MadsRudolph/62768-energy-system/report/sections/responsibility.tex

\ifdefined\mainfile\else\documentclass{article}
\input{../preamble}\begin{document}\fi

\section{Responsibility}
\label{sec:Responsability}

\begin{table}[H]
\centering
\caption{Team responsibilities in the project.}
\renewcommand{\arraystretch}{1.2}

\begin{tabular}{|c|p{8cm}|p{5cm}|}
\hline
\textbf{No.} & \textbf{Tasks} & \textbf{Person} \\
\hline
1 & Design and build the motor-generator setup & All group members \\
\hline
2 & Build and test the rectifier circuit & Nikolas P.L and Nikolas S.J \\
\hline
3 & Design and test the buck converter & Andreas S.J, Jonas B.J and Bjørn A.B  \\
\hline
4 & Design and test the boost converter & Mads R. \\
\hline
5 & Solar panel measurements and MPPT analysis & All group members \\
\hline
6 & Simulink model and PID code generation & Nikolas P.L and Andreas S.J\\
\hline
7 & System integration and final testing & All group members \\
\hline
8 & Report writing and documentation & All group members \\
\hline
\end{tabular}

\label{tab:team_responsibilities}
\end{table}

\ifdefined\mainfile\else\end{document}\fi
