MadsRudolph/62768-energy-system/report/sections/systemoverblik.tex

\ifdefined\mainfile\else\documentclass{article}\input{../preamble}\begin{document}\fi

\section{System overview and requirements}
\label{sec:systemoverblik}
% Overordnet blokdiagram (se TikZ-skabelon nedenfor) + de vigtigste krav (V1/V2/V3).
% Forklar energistrømmen: AC-generator -> transformer -> ensretter -> buck;
% solcelle -> MPPT -> lineær reg -> energilager; boost -> pulserende last.

% --- Skabelon til blokdiagram (udfyld/erstat) ---
\begin{figure}[H]
    \centering
    \begin{tikzpicture}[node distance=2.2cm and 1.6cm]
        \node[block] (gen)  {AC-generator};
        \node[block, right=of gen] (tr) {3$\times$ transformer};
        \node[block, right=of tr] (rec) {Rectifier};
        \node[block, right=of rec] (buck) {Buck 4.8\,V};
        \draw[->] (gen) -- (tr);
        \draw[->] (tr) -- (rec);
        \draw[->] (rec) -- node[above]{V1=15\,V} (buck);
    \end{tikzpicture}
    \caption{Simplified block diagram of the energy system, expanded with PV module/MPPT, energy storage, boost converter, and load).}
    \label{fig:blokdiagram}
\end{figure}

\begin{table}[H]
    \centering
    \begin{tabular}{c l l}
        \toprule
        \textbf{Node} & \textbf{Voltage} & \textbf{Requirement} \\
        \midrule
        V1 & 15\,V $\pm$1\,V  & at 100--300\,mA, hold within for 1.0\,s \\
        V2 & 10\,V $\pm$1\,V  & deliver $\geq$150\,mA, last-step 50--150\,mA \\
        V3 & 5\,V $\pm$0.5\,V & for currents $>$20\,mA \\
        \bottomrule
    \end{tabular}
    \caption{Central voltage specifications. Full list in appendiks~\ref{sec:kravsporing}.}
    \label{tab:krav-overblik}
\end{table}

\ifdefined\mainfile\else\end{document}\fi
