MadsRudolph/62768-energy-system/hardware/kicad/production/motor_power/board_preview_summary.md

# board - board summary

- Size: 104.0 x 104.0 mm
- Copper area: 7995.2 mm^2
- Holes: 181
  - 0.8 mm x 129
  - 1.0 mm x 2
  - 1.1 mm x 29
  - 1.2 mm x 2
  - 1.52 mm x 19
