MadsRudolph/62768-energy-system/docs/Project Specifications.pdf

### KRAVSPECIFIKATION FOR UDVIKLING AF ELEKTRISK ENERGISYSTEM (62768) I 3-UGERS KURSET F2022

Revisionshistorie:

V0: basis specifikation.

V1: Krav 4,5,6 er opdateret / ændret.

V2: Nyt krav om Buck og Boost konvertere er tilføjet.

V3: Krav 5 og 6 er opdateret mht. levering af strøm og belastningen ændringer.

V4: Krav 8-10 opdateret med krav om anvendelse af diskrete komponenter + krav 18 om anvendelse af Arduino platform.

Opgaveoverblik

Der skal udvikles et elektrisk energisystem s om opfylder nedenstående krav. Et blokdiagram over systemet er vist nedenfor.

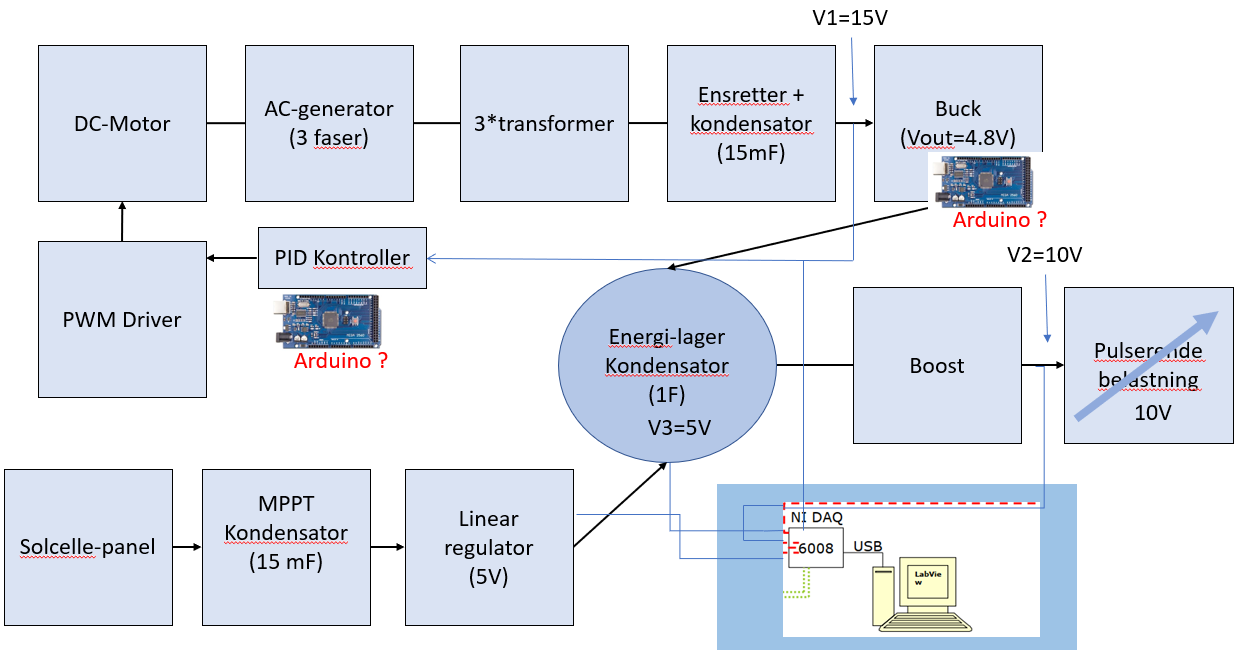
[picture p32: figure]

Krav:

Nummer: | Navn: | Beskrivelse: | Prioritet:
1 | AC-generator spænding (V1) | Den ensrettede spænding på lade-kondensatoren (V1) skal være 15 volt +/- 1 volt. For en buck-strøm på 100 mA | 1
2 | AC-generator strøm | AC-generator systemet skal kunne levere 300 mA til buck konverteren. | 1
3 | AC-generator spænding (V1) under belastning. | Ved en belastningsændring fra 100 mA til 300 mA skal spændingen (V1) overholde krav 1, indenfor 1.0 s. | 1

4 | Belastningsspændingen (V2) | Spændingen V2 skal være indenfor +/- 1.0 volt | 1
5 | Belastningsstrøm (V2) | Spændingskilde V2 skal kunne levere levere min. 150 mA. | 1
6 | Belastningsspændingen (V2) under belastning | Spændingen V2 skal være indenfor +/- 1.0 volt ved en belastningsændring fra 50 mA til 150 mA indenfor 1.0 s. | 1
7 | Energi-lager strøm (V3) | Spændingen V3 skal være indenfor 5 v +/- 0.5 volt ved strømme større end 20 mA . | 1
8 | Spændingskonvertering | Alle spændingskonverteringer skal udføres med egen konstrueret buck/boost konverters. | 1
9 | Spændingskonvertering | Buck/boost konverters og MPPT-systemet skal implementeres med diskrete komponenter. | 1
10 | Strømmåling | Strømmåling kredsløb skal implementeres med diskrete komponenter – ingen integrere kredsløb tilladt (med undtagelse af op-amps).
11 | Energikilde prioritering | Under belastning skal energien fra solcelle-panelet forbruges først. AC-generatoren fungerer således som supplerende energikilde. | 1
12 | Bust og Buck konverter | Skal realiseres som en del af projektet. | 1
13 | Systemovervågning | Et PC-baseret spændingsovervågningssystem udvikles. | 2
14 | Systemovervågning | Spændingsovervågningssystemet opdateres hver 1.0 s. | 2
15 | Muligt software design | Brug Arduinoens ADC, med timer interrupts og PWM | 2
16 | Systemtest | Systemet testes med 100w led light (0.5 meter) fra solpanelet | 1
17 | Lineær regulator | Må udskiftes med en buck regulator | 2
18 | Data behandlingsplatform | Arduino | 2

Prioritet:

1: Skal designes og implementeres

2: Frivilligt om disse krav medtages.
