MadsRudolph/62768-energy-system/report/sections/konklusion.tex

\ifdefined\mainfile\else\documentclass{article}\input{../preamble}\begin{document}\fi

\vspace{3cm}

\section{Conclusion}
\label{sec:konklusion}
From the entire project, we can conclude that we have developed a functional system, with all sub-components implemented as intended.\\
Although the system does not operate perfectly, we have successfully created a \textit{proof-of-concept} that demonstrates the interaction between the individual subsystems and validates the overall design.\\
Each converter fulfills its intended purpose, the MPPT operates as expected, and the rectifier correctly converts the AC input to DC. The system has been tested, and the main specifications have been verified.\\
However, inaccuracies and inefficiencies were observed, particularly in the switching behavior and control, which can be attributed to non-ideal components and limitations in the implemented control strategy.\\
This highlights the importance of proper regulation, component selection, and system integration in power electronics design.\\
In conclusion, the system works as intended on a conceptual level, and with further optimization and improved control, it has the potential to become significantly more stable and efficient.
% Opsummering: hvad blev opnået, hvilke krav er opfyldt.

% TODO.

\ifdefined\mainfile\else\end{document}\fi
