MadsRudolph/62768-energy-system/hardware/production/system/sessions/MegaPCB_top_probe_grid.csv

x_mm | y_mm | dz_mm
9.071 | 11.953 | 0
103.550 | 11.953
198.529 | 11.953
9.071 | 72.416
103.550 | 72.416
198.529 | 72.416
9.071 | 131.378
103.550 | 131.378
198.529 | 131.378
