MadsRudolph/62768-energy-system/hardware/kicad/simulation/exp3a/fb_sweep.csv

INPUT_V | FB_OUT_V
0.0 | 0.000150
0.5 | 0.083397
1.0 | 0.166720
1.5 | 0.250047
2.0 | 0.333376
2.5 | 0.416705
3.0 | 0.500035
3.5 | 0.583365
4.0 | 0.666696
4.5 | 0.750027
5.0 | 0.833358
5.5 | 0.916689
6.0 | 1.000020
6.5 | 1.083351
7.0 | 1.166683
7.5 | 1.250014
8.0 | 1.333346
8.5 | 1.416677
9.0 | 1.500009
9.5 | 1.583340
10.0 | 1.666672
10.5 | 1.750004
11.0 | 1.833335
11.5 | 1.916667
12.0 | 1.999999
12.5 | 2.083330
13.0 | 2.166662
13.5 | 2.249994
14.0 | 2.333325
14.5 | 2.416657
15.0 | 2.499988
