MadsRudolph/62768-energy-system/hardware/kicad/boards/boost/pcb/boost_bottom.png

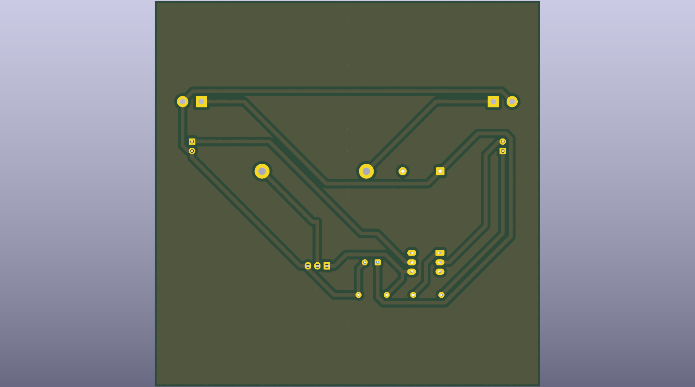
hardware/kicad/boards/boost/pcb/boost_bottom.png
