MadsRudolph/62768-energy-system/hardware/kicad/boards/boost/pcb/boost_top.png

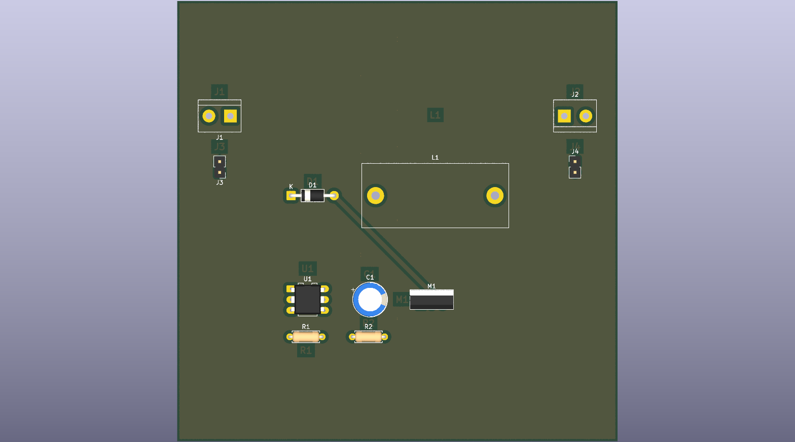
hardware/kicad/boards/boost/pcb/boost_top.png
