MadsRudolph/62768-energy-system/hardware/kicad/boards/buck/buck_v2/pcb/buck_v2_top.png

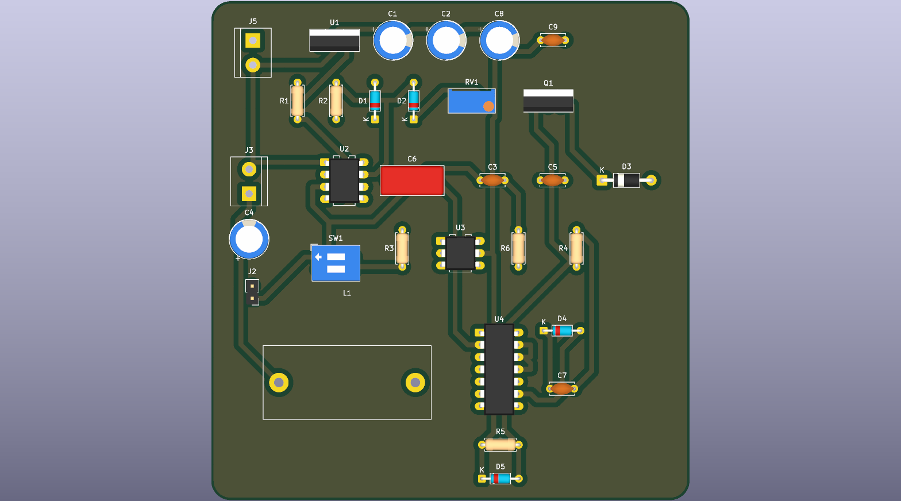
hardware/kicad/boards/buck/buck_v2/pcb/buck_v2_top.png
