MadsRudolph/62768-energy-system/hardware/kicad/boards/buck/pcb/buck_top.png

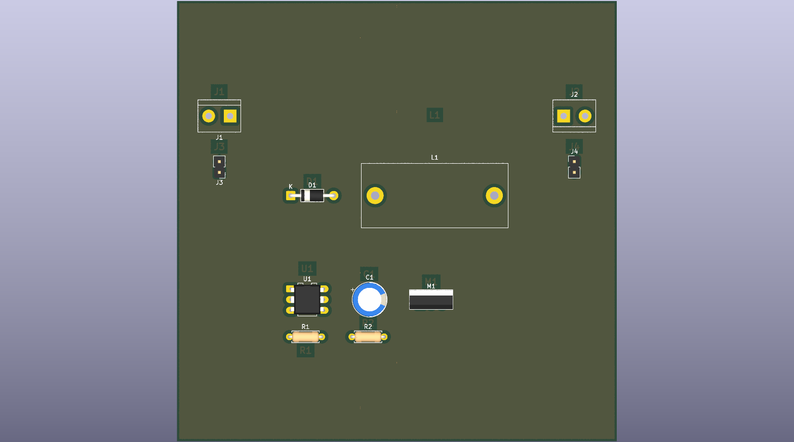
hardware/kicad/boards/buck/pcb/buck_top.png
