MadsRudolph/62768-energy-system/hardware/kicad/boards/current_sense/pcb/current_sense_bottom.png

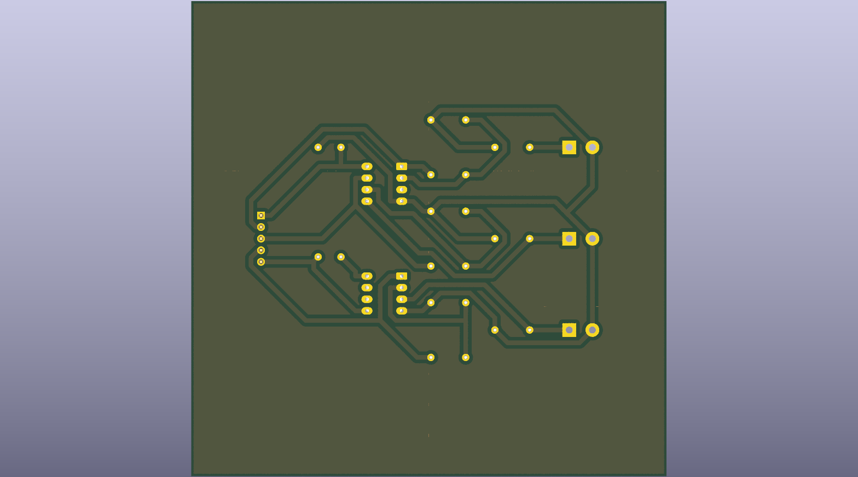
hardware/kicad/boards/current_sense/pcb/current_sense_bottom.png
