MadsRudolph/62768-energy-system/hardware/kicad/boards/current_sense/pcb/current_sense_top.png

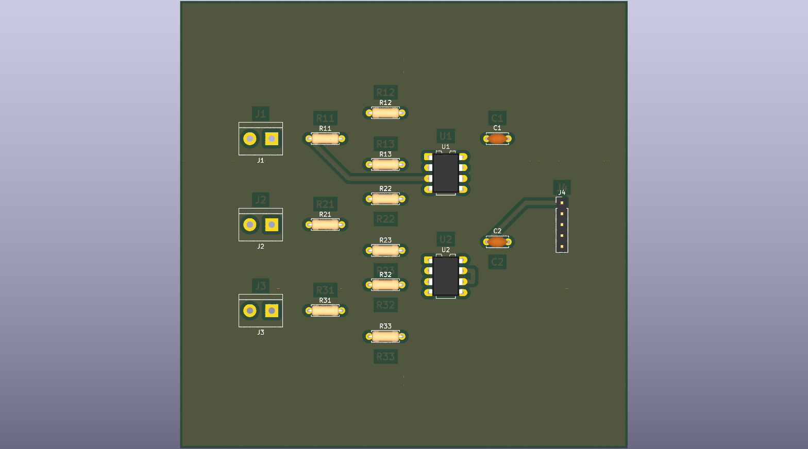
hardware/kicad/boards/current_sense/pcb/current_sense_top.png
