MadsRudolph/62768-energy-system/hardware/kicad/boards/drive_circuit/pcb/drive_circuit_bottom.png

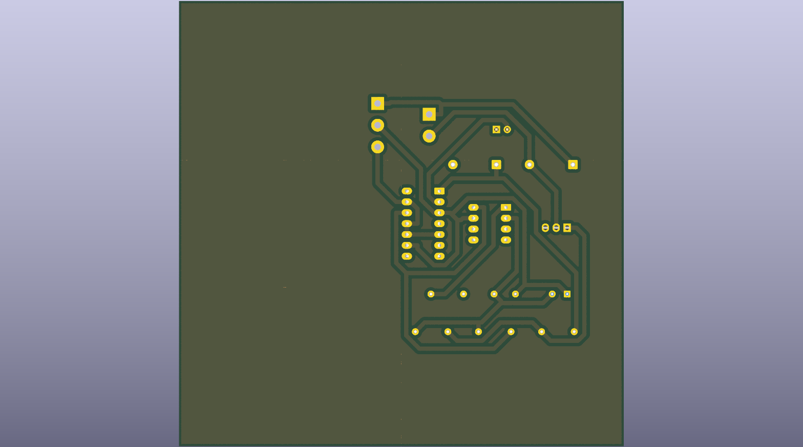
hardware/kicad/boards/drive_circuit/pcb/drive_circuit_bottom.png
