MadsRudolph/62768-energy-system/hardware/kicad/boards/feedback_circuit/pcb/feedback_circuit_bottom.png

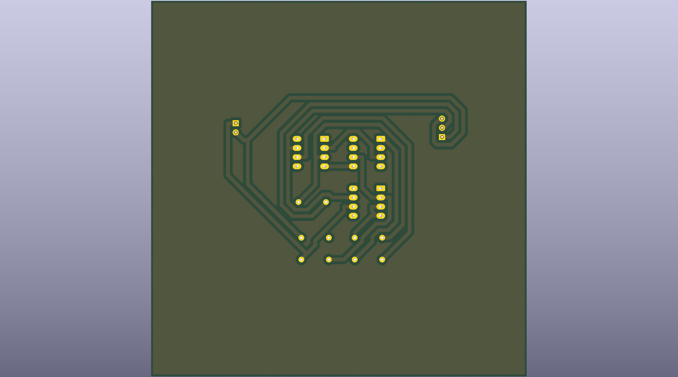
hardware/kicad/boards/feedback_circuit/pcb/feedback_circuit_bottom.png
