MadsRudolph/62768-energy-system/hardware/kicad/boards/mppt/pcb/mppt_top.png

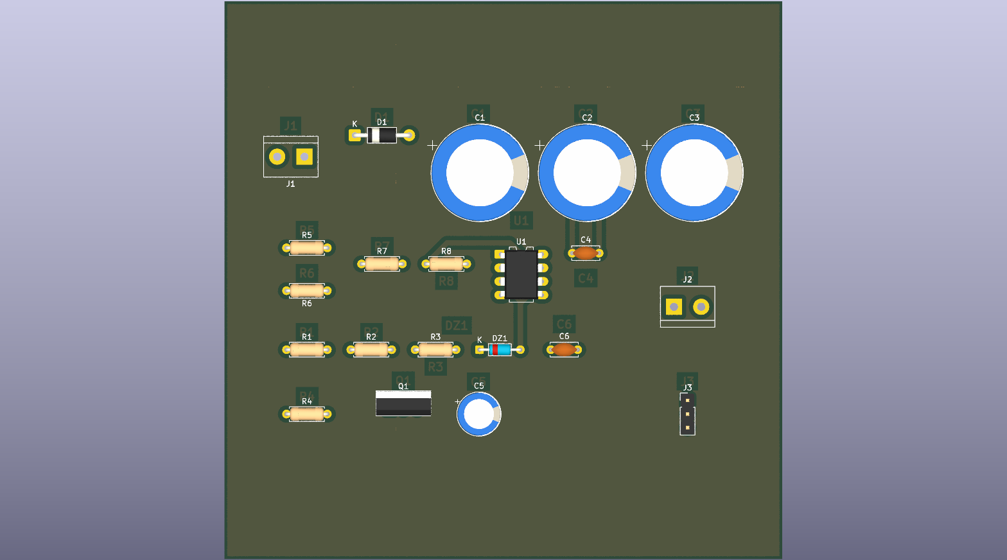
hardware/kicad/boards/mppt/pcb/mppt_top.png
