MadsRudolph/62768-energy-system/hardware/kicad/boards/rectifier/pcb/rectifier_top.png

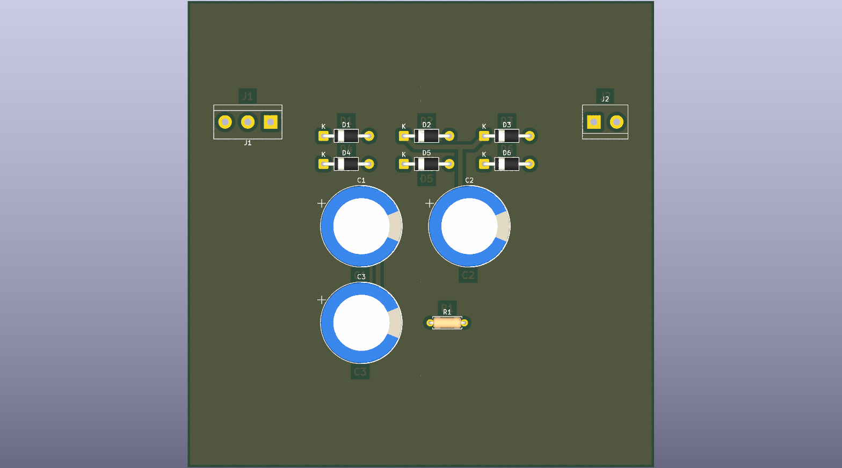
hardware/kicad/boards/rectifier/pcb/rectifier_top.png
