MadsRudolph/62768-energy-system/hardware/kicad/production/motor_power/board_preview.png

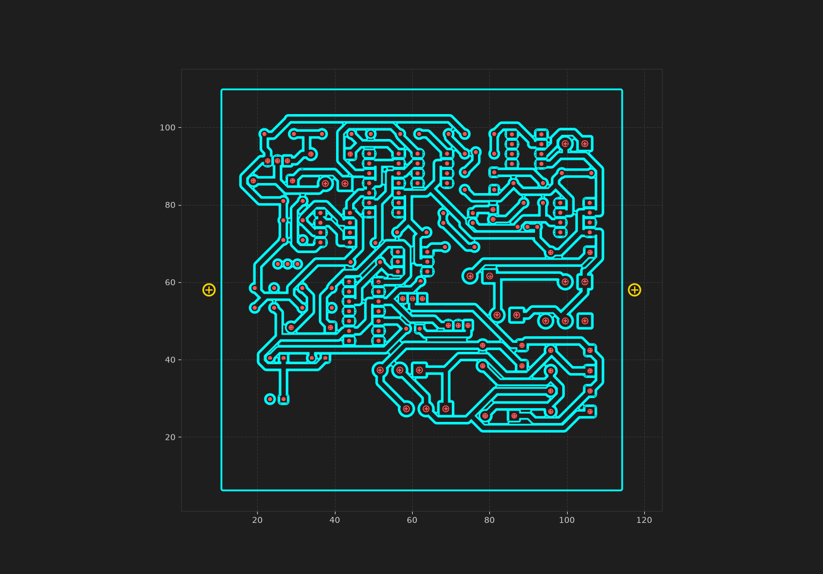
hardware/kicad/production/motor_power/board_preview.png
