MadsRudolph/62768-energy-system/hardware/kicad/simulation/exp3a/drive_waveforms.png

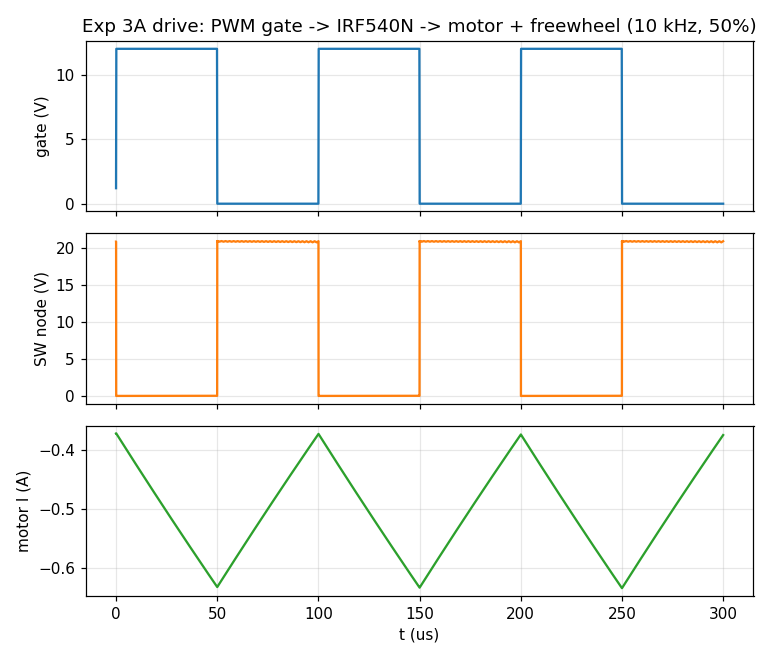
hardware/kicad/simulation/exp3a/drive_waveforms.png
