MadsRudolph/62768-energy-system/hardware/kicad/simulation/exp3a/fb_transfer.png

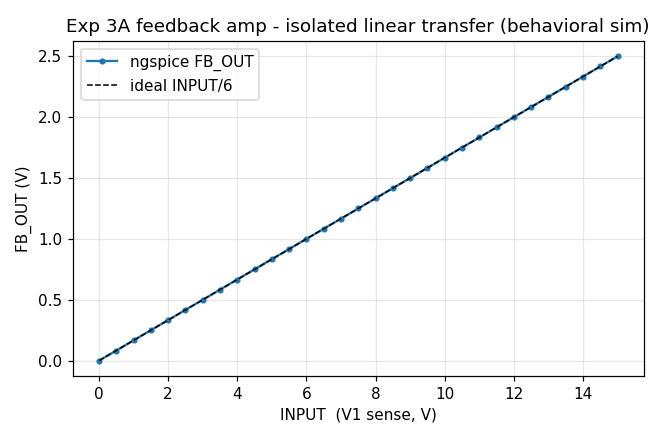
hardware/kicad/simulation/exp3a/fb_transfer.png
