MadsRudolph/62768-energy-system/report/images/Blokdiagram/Motor_circuit_blokdiagram.png

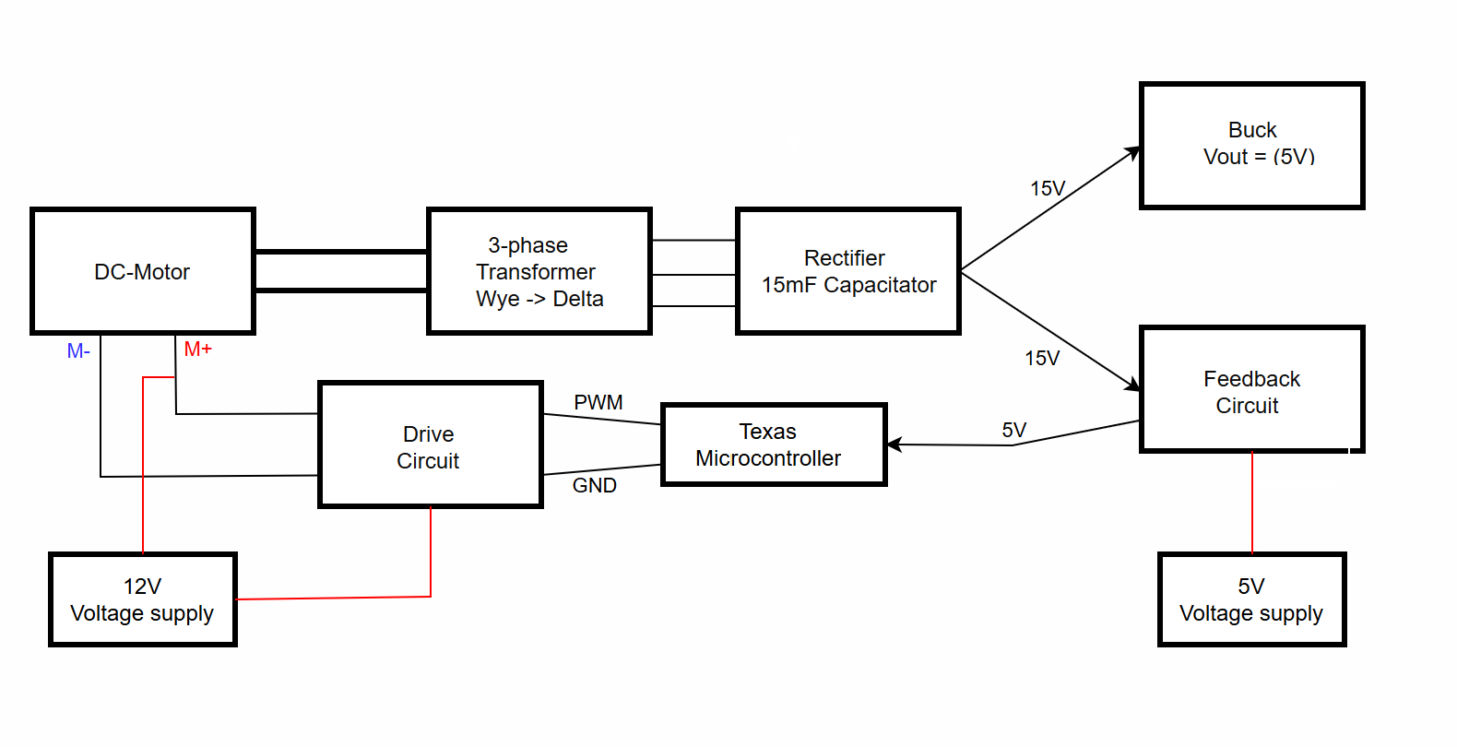
report/images/Blokdiagram/Motor_circuit_blokdiagram.png
