MadsRudolph/62768-energy-system/report/images/MPPT/PWM simulation.png

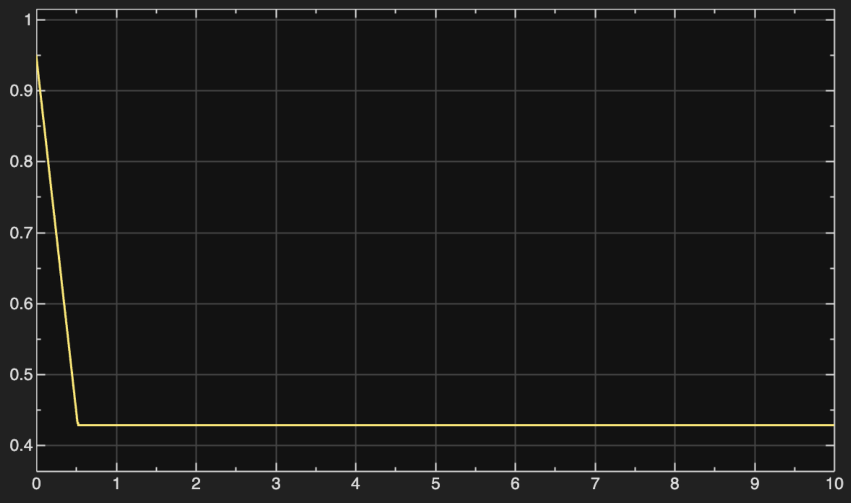
report/images/MPPT/PWM simulation.png
