MadsRudolph/62768-energy-system/report/images/Solarpanel/PV-curve of PV module.png

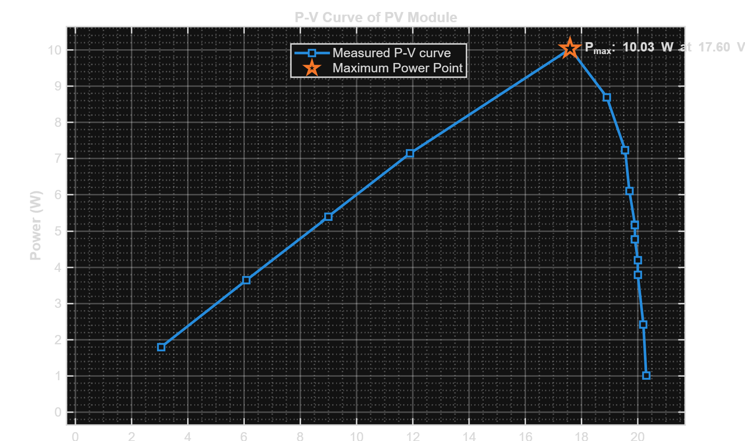
report/images/Solarpanel/PV-curve of PV module.png
