MadsRudolph/62768-energy-system/hardware/kicad/production/drive_circuit/drive_circuit.dxf

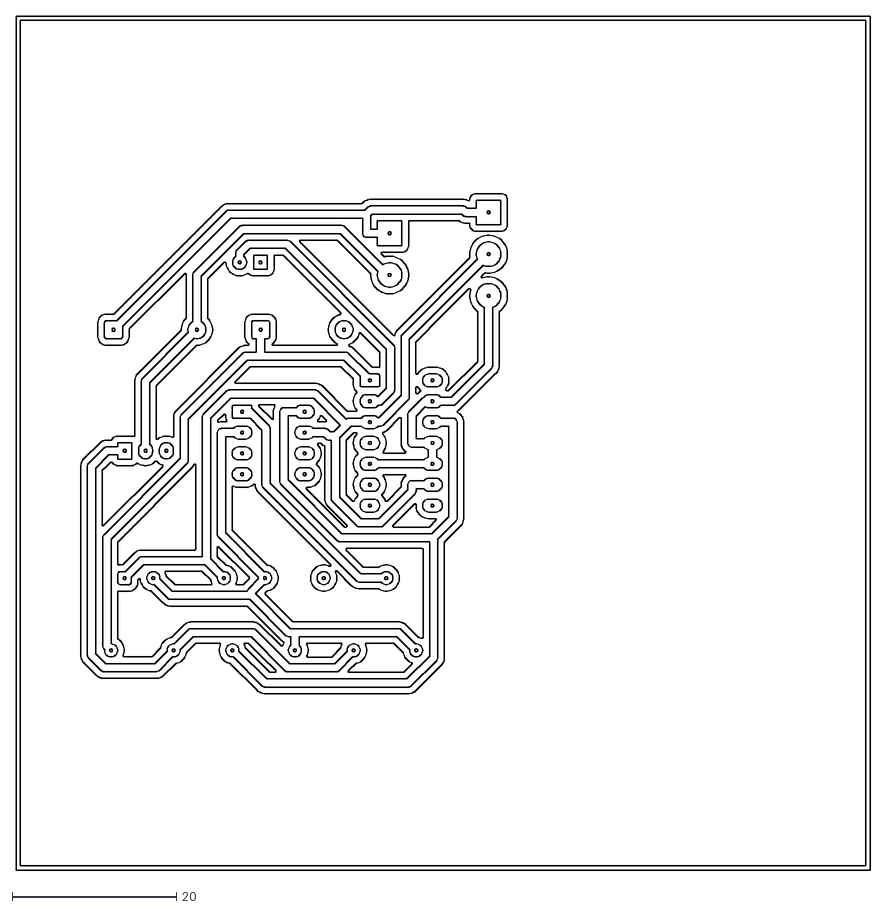
[picture p72: CAD file, 2026-06-11]
hardware/kicad/production/drive_circuit/drive_circuit.dxf
104.0 x 104.0
