MadsRudolph/62768-energy-system/hardware/kicad/production/mppt/mppt.dxf

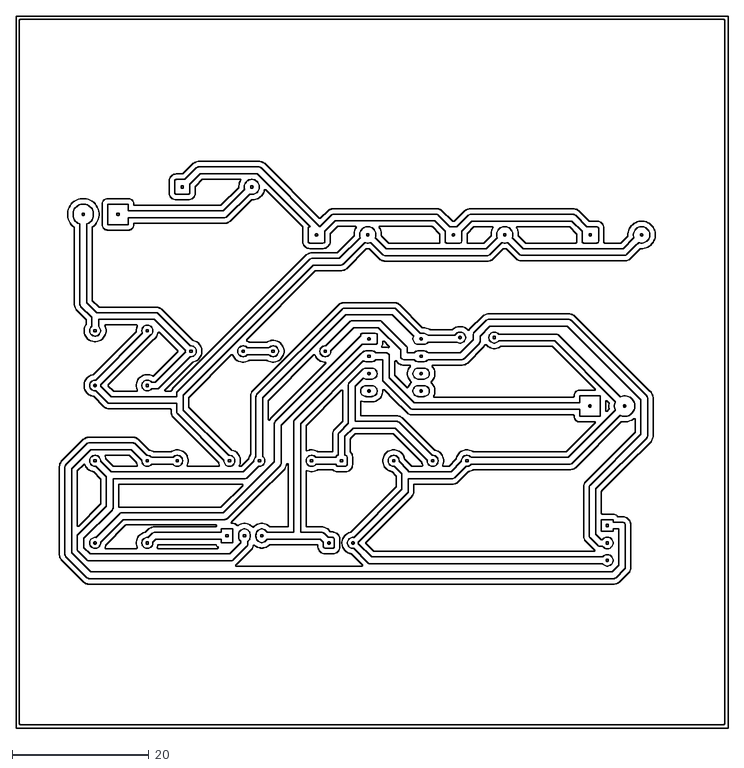
[picture p74: CAD file, 2026-06-11]
hardware/kicad/production/mppt/mppt.dxf
104.0 x 104.0
