MadsRudolph/62768-energy-system/hardware/kicad/production/mppt_buck/mppt_buck.dxf

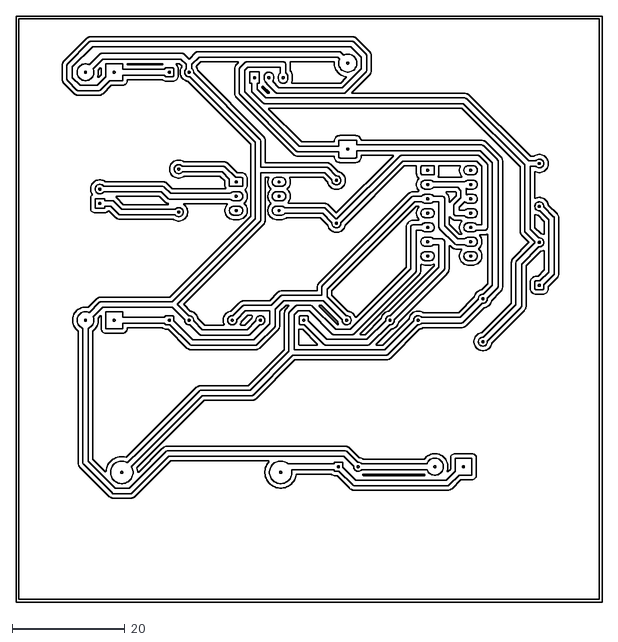
[picture p75: CAD file, 2026-06-18]
hardware/kicad/production/mppt_buck/mppt_buck.dxf
104.0 x 104.0
