MadsRudolph/62768-energy-system/hardware/kicad/production/rectifier/rectifier.dxf

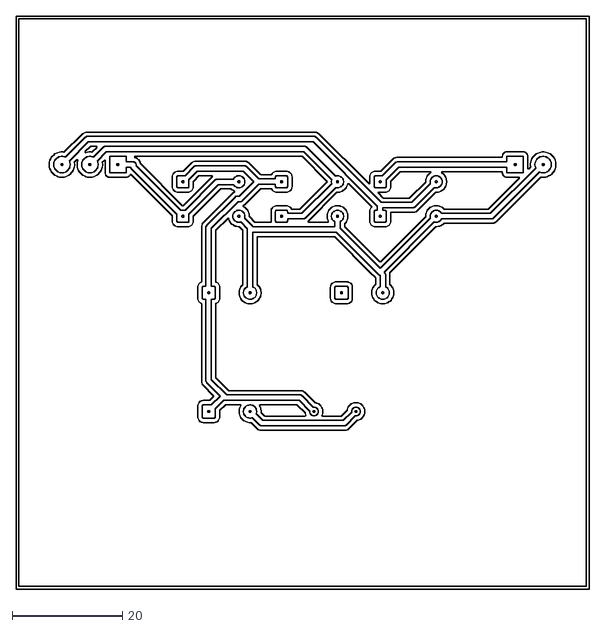
[picture p76: CAD file, 2026-06-11]
hardware/kicad/production/rectifier/rectifier.dxf
104.0 x 104.0
