MadsRudolph/62768-energy-system/hardware/kicad/production/buck_v2/buck_v2_holes.dxf

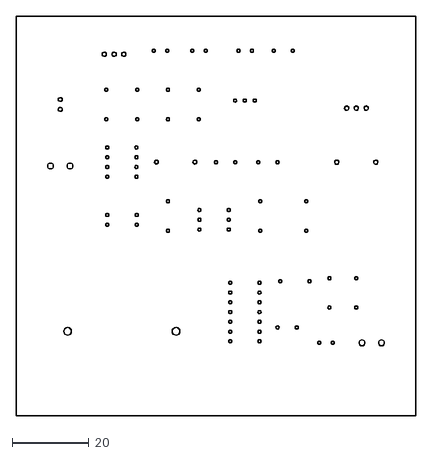
[picture p77: CAD file, 2026-06-18]
hardware/kicad/production/buck_v2/buck_v2_holes.dxf
104.0 x 104.0
