MadsRudolph/62768-energy-system/hardware/kicad/production/c2000_feedback/c2000_feedback.dxf

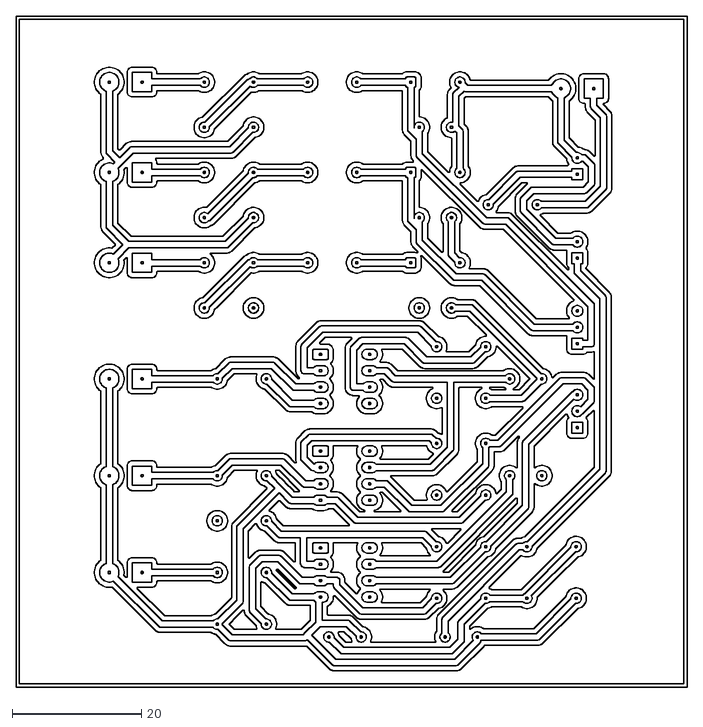
[picture p78: CAD file, 2026-06-18]
hardware/kicad/production/c2000_feedback/c2000_feedback.dxf
104.0 x 104.0
