MadsRudolph/62768-energy-system/hardware/kicad/production/current_sense/current_sense_top_cu.dxf

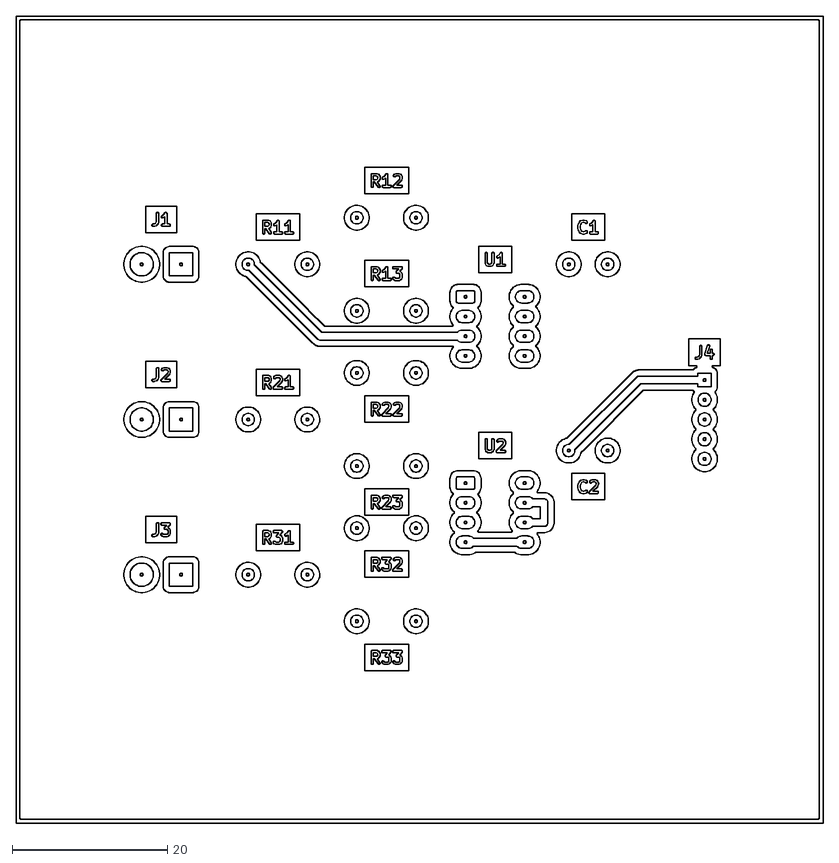
[picture p79: CAD file, 2026-06-11]
hardware/kicad/production/current_sense/current_sense_top_cu.dxf
104.0 x 104.0
