MadsRudolph/62768-energy-system/hardware/kicad/production/drive_circuit/drive_circuit_top_cu.dxf

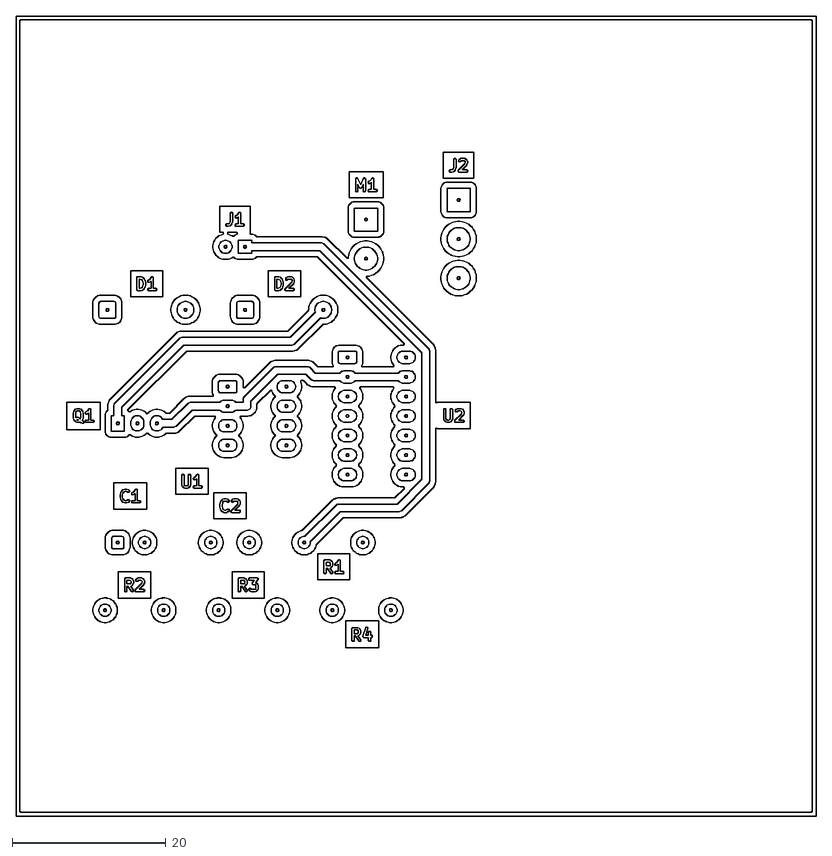
[picture p80: CAD file, 2026-06-11]
hardware/kicad/production/drive_circuit/drive_circuit_top_cu.dxf
104.0 x 104.0
