MadsRudolph/62768-energy-system/hardware/kicad/production/mppt_buck/mppt_buck_top_cu.dxf

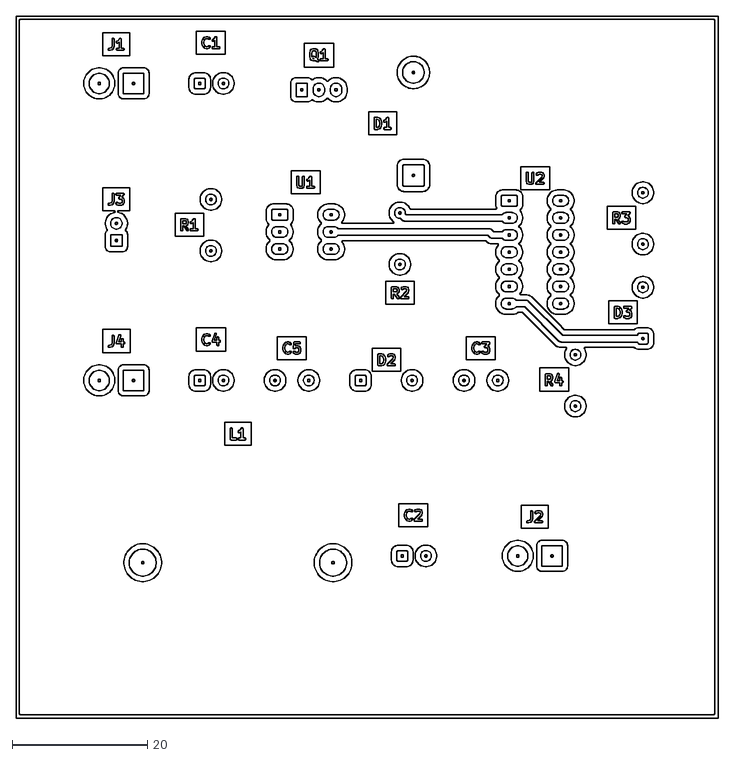
[picture p83: CAD file, 2026-06-18]
hardware/kicad/production/mppt_buck/mppt_buck_top_cu.dxf
104.0 x 104.0
