MadsRudolph/62768-energy-system/hardware/kicad/production/rectifier/rectifier_top_cu.dxf

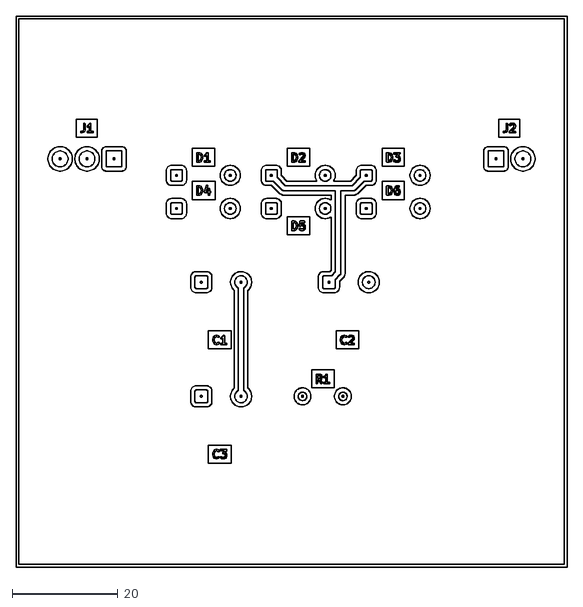
[picture p84: CAD file, 2026-06-11]
hardware/kicad/production/rectifier/rectifier_top_cu.dxf
104.0 x 104.0
