MadsRudolph/62768-energy-system/hardware/kicad/production/buck_v2/buck_v2_silk_top.dxf

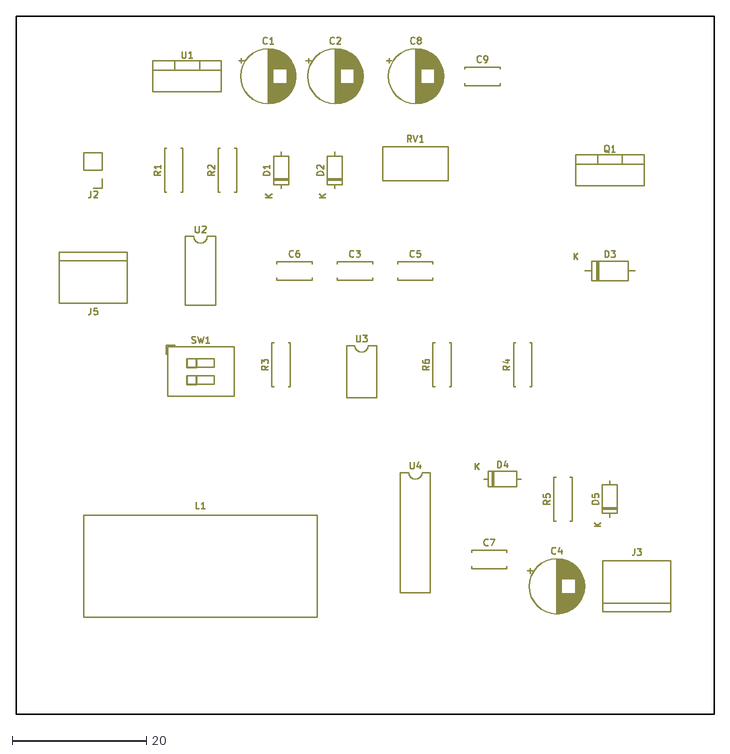
[picture p85: CAD file, 2026-06-18]
hardware/kicad/production/buck_v2/buck_v2_silk_top.dxf
104.0 x 104.0
