MadsRudolph/62768-energy-system/report/sections/test.tex

\ifdefined\mainfile\else\documentclass{article}\input{../preamble}\begin{document}\fi

\section{Test ans resultats}
\label{sec:test}
% Systemtest: 100 W LED-lys (0.5 m) drevet fra solcellepanelet (krav 16).
% Saml måleresultater (data i ../measurements/) og sammenlign med kravene.

% TODO: målemetode, resultater, tabeller/grafer, kravopfyldelse.

\ifdefined\mainfile\else\end{document}\fi
