MadsRudolph/62768-energy-system/measurements/Motortest ver3_Ny generator.xlsx

Sheet: lille motor
power supply |  |  | Generator | load 10 Ω |  |  | 14 p
U | I | Power | U | Power | Virkningsgrad | frekvens | omdr |  | U/f*1000
[V] | [A] | [W] | [V] | [W] | [%] | [Hz] | [rev/min]
12.5 | 3.09 | 38.62 | 7.11 | 15.17 | 39.3 | 1055 | 9042.857143 |  | 6.739
11.0 | 2.74 | 30.14 | 6.32 | 11.98 | 39.8 | 990.4 | 8489.142857 |  | 6.381
9.5 | 2.46 | 23.37 | 5.61 | 9.44 | 40.4 | 871 | 7465.714286 |  | 6.441
8.0 | 2.13 | 17.04 | 4.73 | 6.71 | 39.4 | 737.7 | 6323.142857 |  | 6.412
6.5 | 1.79 | 11.63 | 3.84 | 4.42 | 38.0 | 596 | 5108.571429 |  | 6.443
5.0 | 1.45 | 7.25 | 2.96 | 2.63 | 36.2 | 459.8 | 3941.142857 |  | 6.435
3.5 | 1.08 | 3.78 | 1.95 | 1.14 | 30.3 | 303.5 | 2601.428571 |  | 6.435
power supply |  |  | Generator | load 22 Ω |  |  | 14 p
U | I | Power | U | Power | Virkningsgrad | frekvens | omdr |  | U/f*1000
[V] | [A] | [W] | [V] | [W] | [%] | [Hz] | [rev/min]
12.5 | 2.23 | 27.88 | 8.84 | 10.66 | 38.2 | 1357 | 11631.42857 |  | 6.514
11.0 | 1.99 | 21.89 | 7.95 | 8.62 | 39.4 | 1213 | 10397.14286 |  | 6.554
9.5 | 1.76 | 16.72 | 6.90 | 6.49 | 38.8 | 1051 | 9008.571429 |  | 6.565
8.0 | 1.51 | 12.08 | 5.75 | 4.51 | 37.3 | 880.8 | 7549.714286 |  | 6.528
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
