MadsRudolph/62768-energy-system/simulation/rectifier_result.png

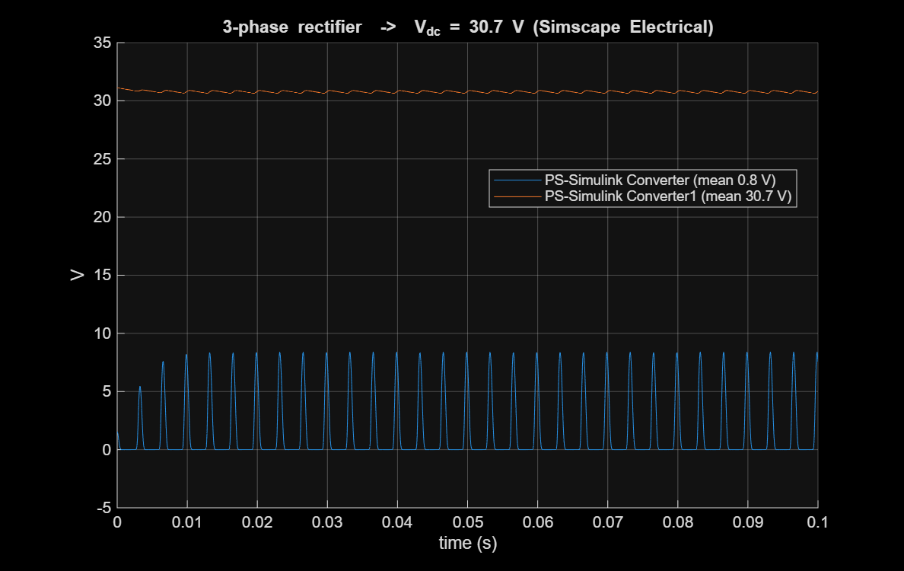
simulation/rectifier_result.png
