MadsRudolph/62768-energy-system/simulation/ltspice/BUCK.asc

C1: cap; 4.7µ
D1: diode; Dsch
L1: ind; 31.7m
R1: res; 50
S1: sw
V1: voltage; 15
V2: voltage; PULSE(0 5 0 10n 10n 3.3u 10u)
Named nets: 0
.tran 100m
.model SW SW (Vt=2 Ron=0.1 Roff=1MEG)
.model Dsch D(Is=1u Rs=0.05 N=1.05 Cjo=100p)
