MadsRudolph/62768-energy-system/firmware/MPPT-embedded-c/src/twi.h

#ifndef TWI_H
#define TWI_H

#include <stdint.h>

void TWI_init(void);
void TWI_start(void);
void TWI_stop(void);
void TWI_write(uint8_t data);
uint8_t TWI_read_ack(void);
uint8_t TWI_read_nack(void);

#endif
